w5xd/RC1101/PCBpartial.jpg

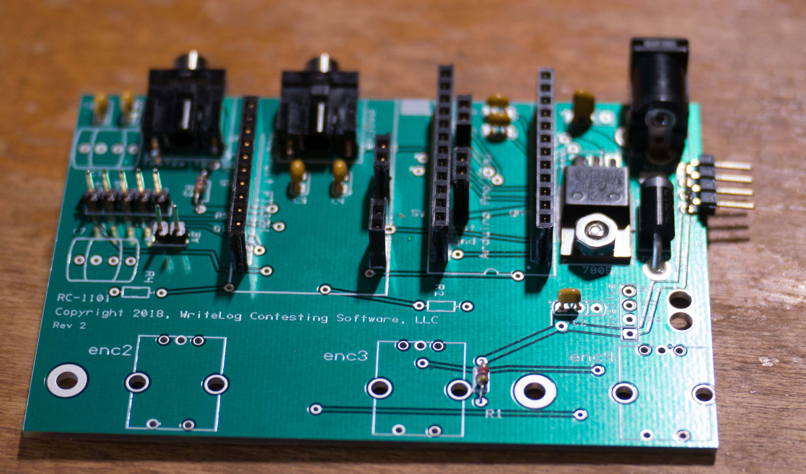
PCBpartial.jpg
