w5xd/RC1101/CAD/Trellis/Overlay-Blank.stp

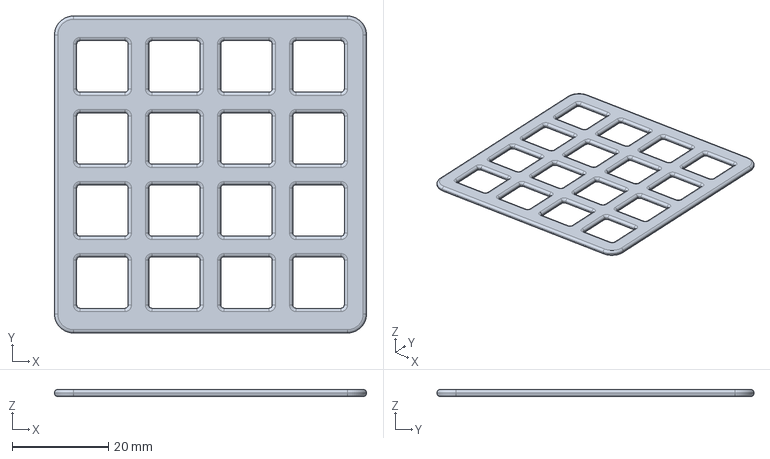
[picture p26: CAD file, 2024-01-12]
CAD/Trellis/Overlay-Blank.stp
65.0 x 66.0 x 1.50 mm
