w5xd/RC1101/STL/Overlay-Generic.STL

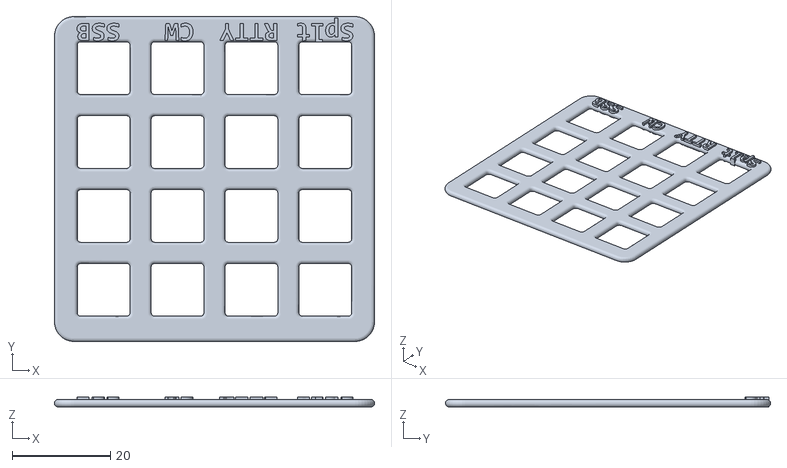
[picture p27: CAD file, 2022-08-31]
STL/Overlay-Generic.STL
65.0 x 66.0 x 2.00
