w5xd/RC1101/CAD/Adafruit232H/StandingOff.SLDPRT

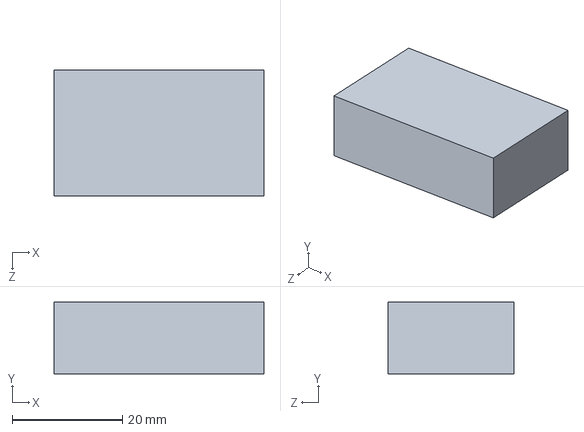
[picture p28: CAD file, 2020-03-09]
CAD/Adafruit232H/StandingOff.SLDPRT
38.1 x 13.0 x 22.9 mm
