w5xd/RC1101/CAD/Enclosure/enclosure2 LCD back cover.sldprt

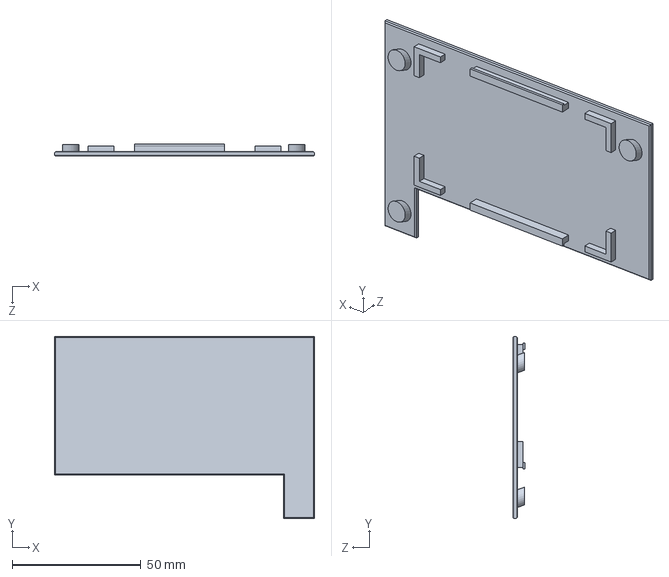
[picture p29: CAD file, 2019-06-19]
CAD/Enclosure/enclosure2 LCD back cover.sldprt
101.0 x 70.7 x 4.75 mm
