w5xd/RC1101/CAD/knobs/SmallKnob.SLDPRT

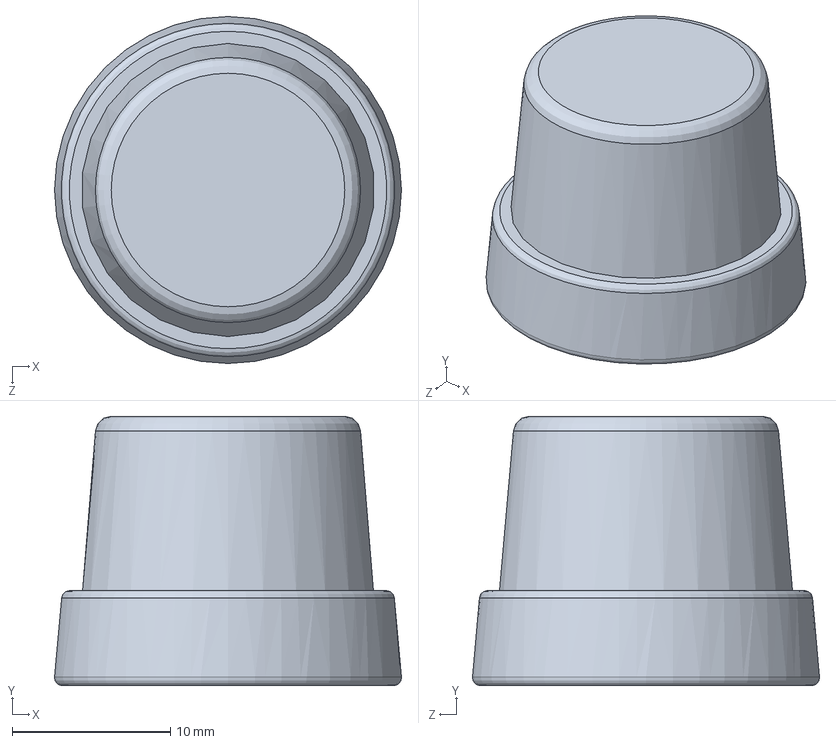
[picture p30: CAD file, 2019-06-19]
CAD/knobs/SmallKnob.SLDPRT
21.9 x 17.0 x 21.9 mm
