w5xd/RC1101/CAD/PCB/puiaudio.SLDPRT

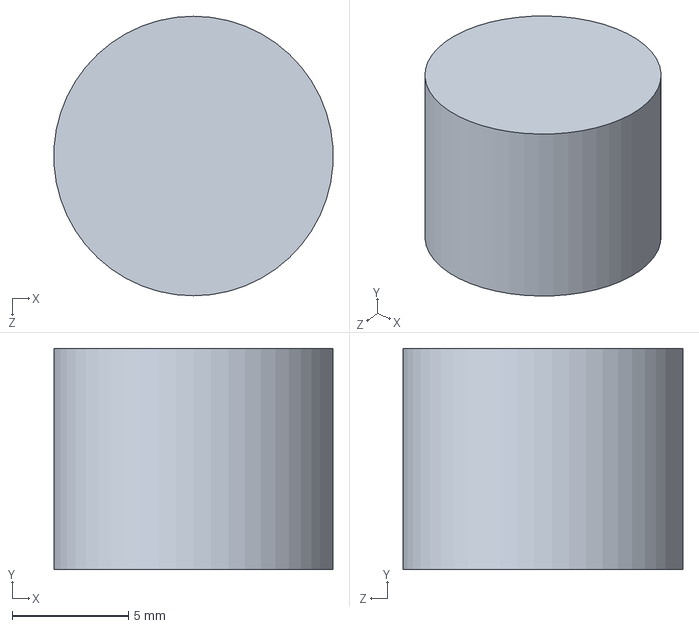
[picture p31: CAD file, 2019-06-19]
CAD/PCB/puiaudio.SLDPRT
12.0 x 9.50 x 12.0 mm
