w5xd/RC1101/CAD/pec12/pec12-encoder.SLDPRT

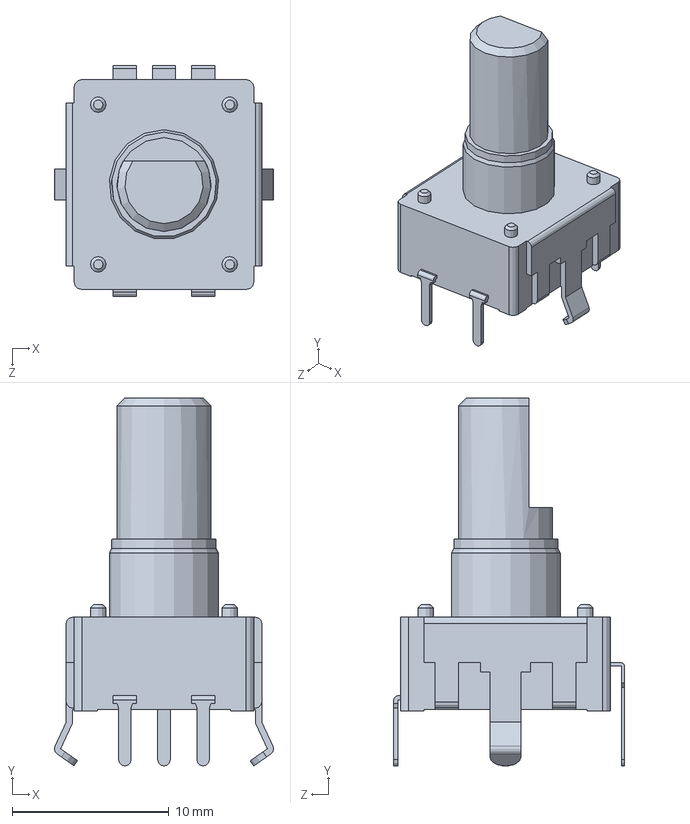
[picture p32: CAD file, 2019-06-19]
CAD/pec12/pec12-encoder.SLDPRT
14.0 x 23.5 x 14.8 mm
