w5xd/RC1101/CAD/TO220/274-2AB HEATSINK LOW HEIGHT BLK TO-220.SLDPRT

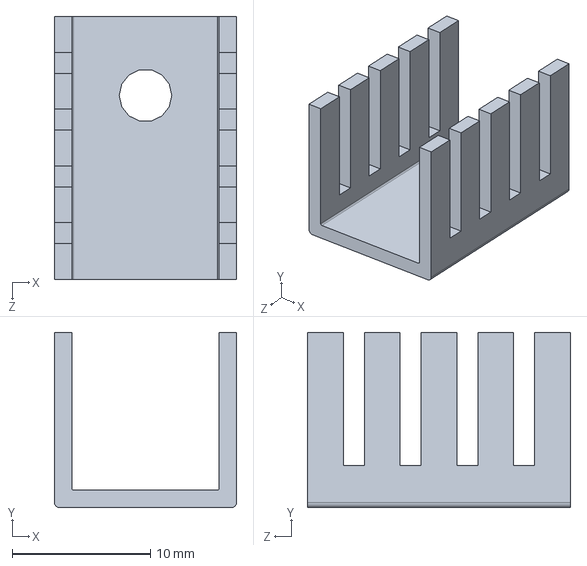
[picture p33: CAD file, 2018-12-13]
CAD/TO220/274-2AB HEATSINK LOW HEIGHT BLK TO-220.SLDPRT
13.2 x 12.7 x 19.1 mm
