w5xd/RC1101/CAD/Enclosure/enclosure2 bottom cover.sldprt

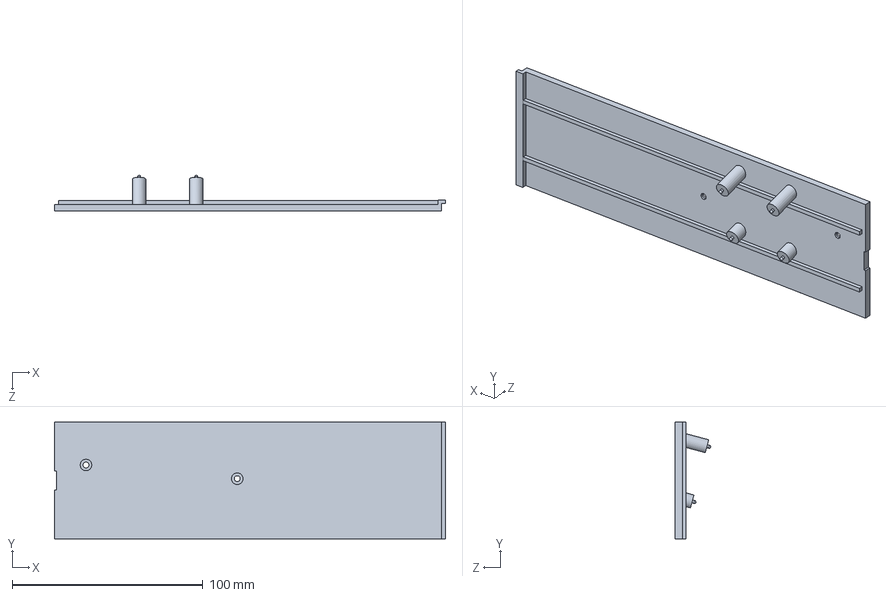
[picture p35: CAD file, 2019-06-19]
CAD/Enclosure/enclosure2 bottom cover.sldprt
205.2 x 61.2 x 18.7 mm
