w5xd/RC1101/CAD/PCB/5PinLcd.SLDPRT

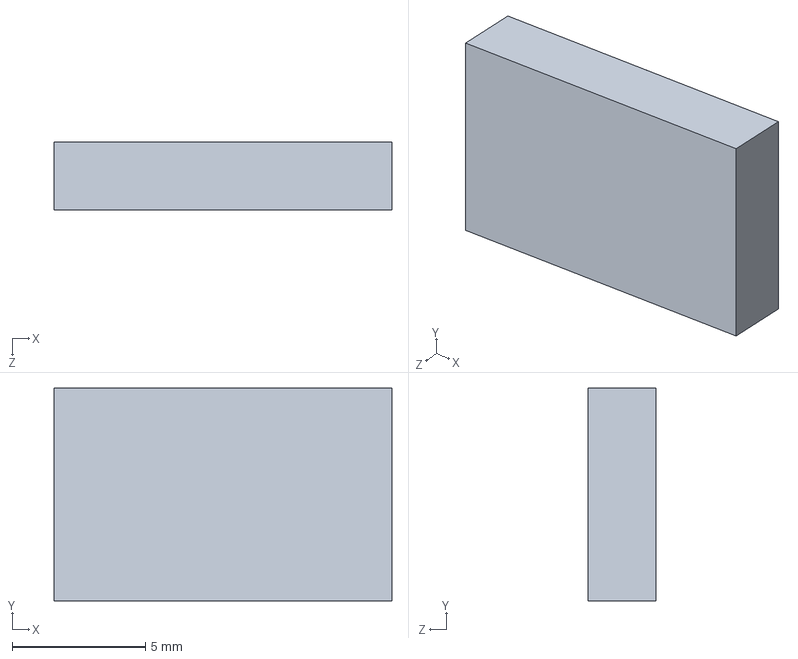
[picture p36: CAD file, 2019-06-19]
CAD/PCB/5PinLcd.SLDPRT
12.7 x 8.00 x 2.54 mm
