w5xd/RC1101/CAD/pec12/CUI_PJ-202A.sldprt

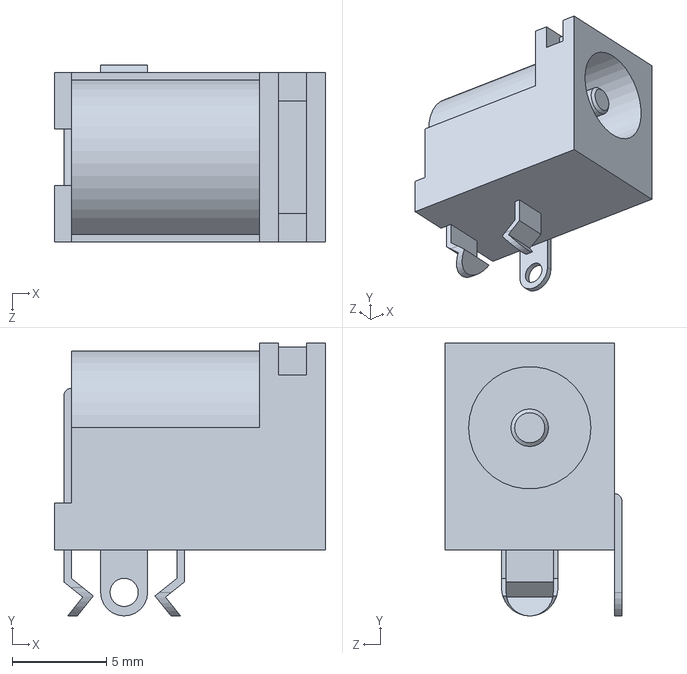
[picture p37: CAD file, 2019-06-19]
CAD/pec12/CUI_PJ-202A.sldprt
14.4 x 14.5 x 9.40 mm
