w5xd/RC1101/CAD/Trellis/Overlay-Icom.SLDPRT

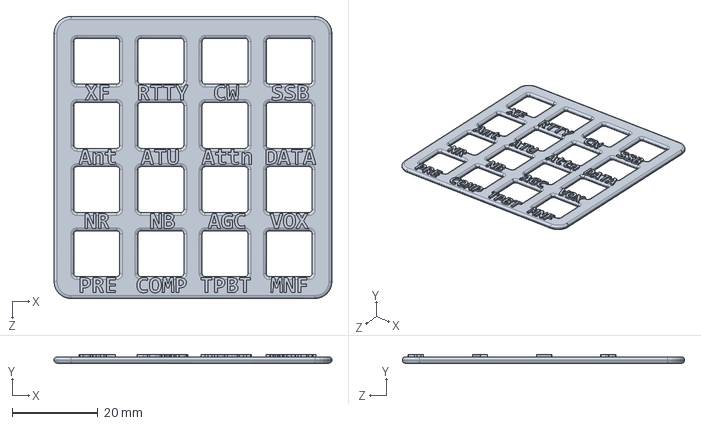
[picture p38: CAD file, 2022-08-31]
CAD/Trellis/Overlay-Icom.SLDPRT
65.0 x 2.00 x 66.0 mm
