w5xd/RC1101/CAD/Adafruit232H/quiik.stp

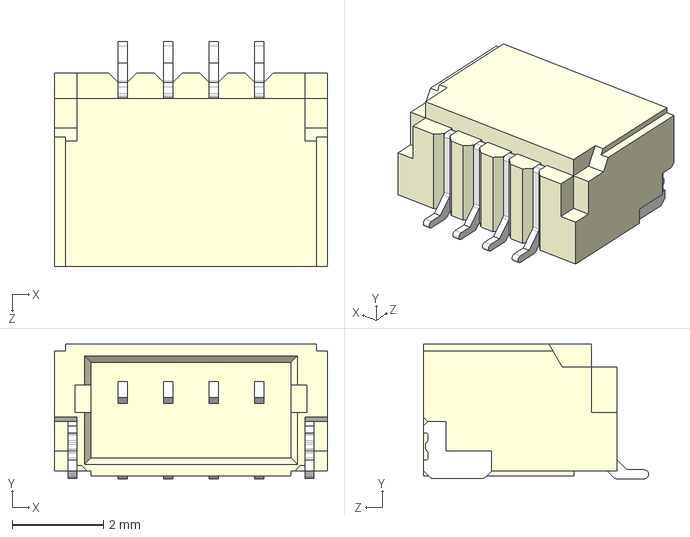
[picture p39: CAD file, 2020-03-09]
CAD/Adafruit232H/quiik.stp
6.00 x 2.96 x 4.95 mm
