w5xd/RC1101/CAD/LCD/gen4/4DLCD-32T-QVGA-LCDGLASS.sldprt

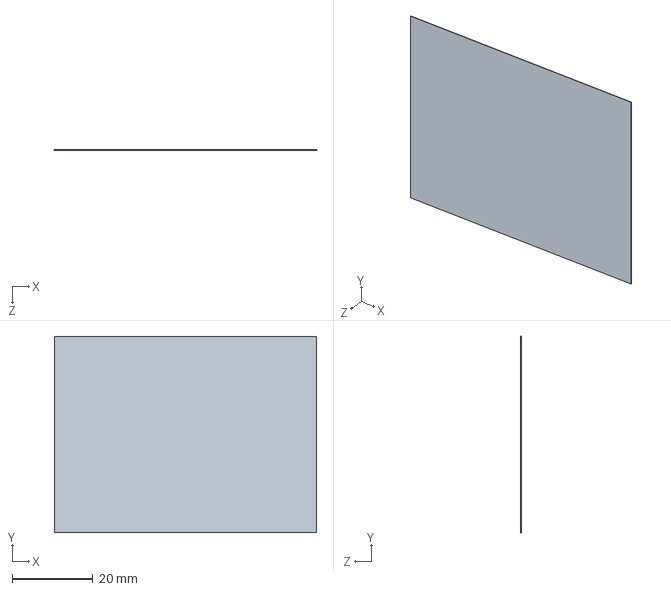
[picture p40: CAD file, 2019-06-19]
CAD/LCD/gen4/4DLCD-32T-QVGA-LCDGLASS.sldprt
64.8 x 48.6 x 0.1 mm
