w5xd/RC1101/CAD/PCB/Enc1Header.SLDPRT

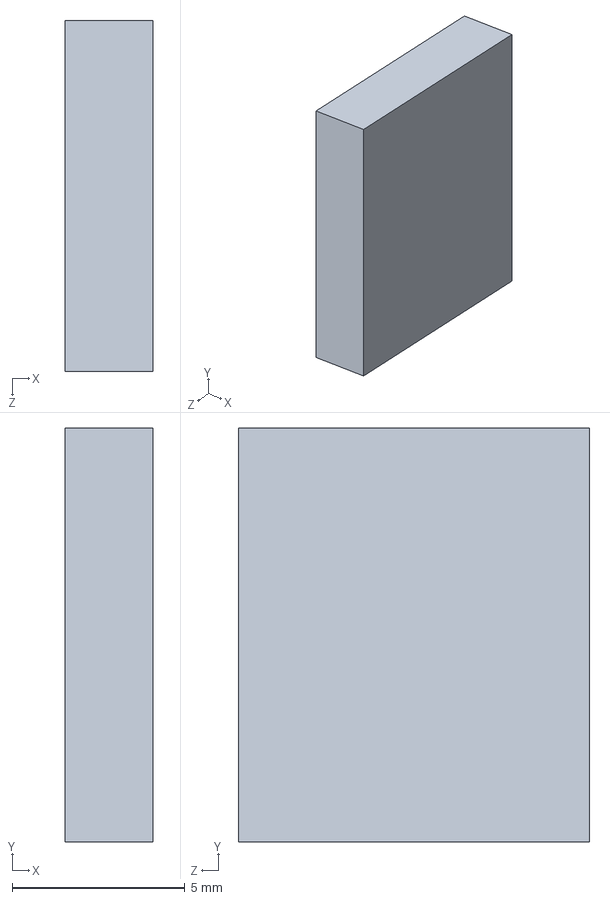
[picture p41: CAD file, 2019-06-19]
CAD/PCB/Enc1Header.SLDPRT
2.54 x 12.0 x 10.2 mm
