w5xd/RC1101/CAD/Adafruit232H/pcb-ft232.SLDPRT

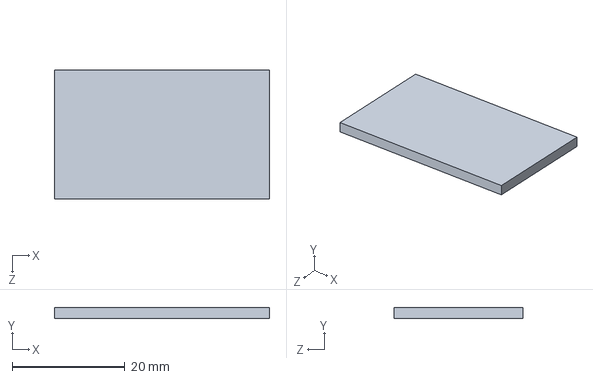
[picture p42: CAD file, 2020-03-09]
CAD/Adafruit232H/pcb-ft232.SLDPRT
38.1 x 2.00 x 22.9 mm
