w5xd/RC1101/CAD/PCB/gen4-ib.SLDPRT

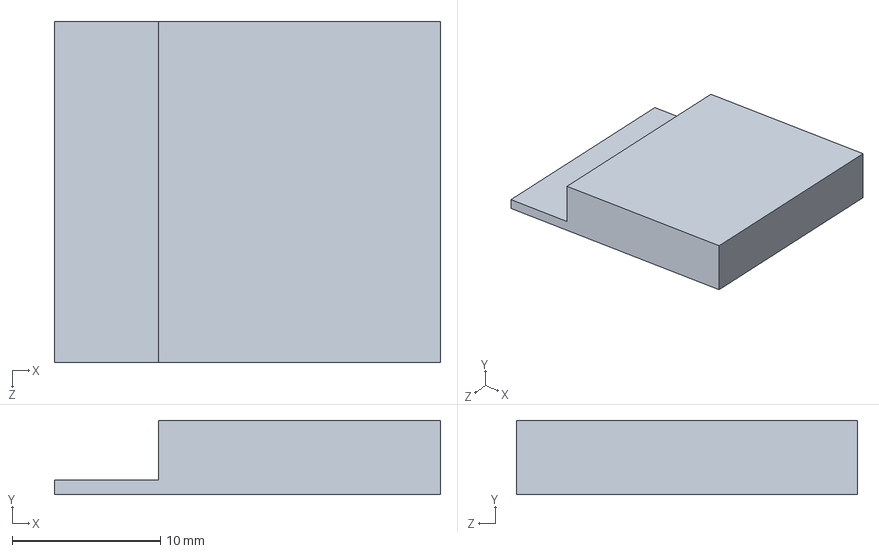
[picture p43: CAD file, 2019-06-19]
CAD/PCB/gen4-ib.SLDPRT
26.0 x 5.00 x 23.0 mm
