w5xd/RC1101/CAD/Adafruit232H/USB-C.stp

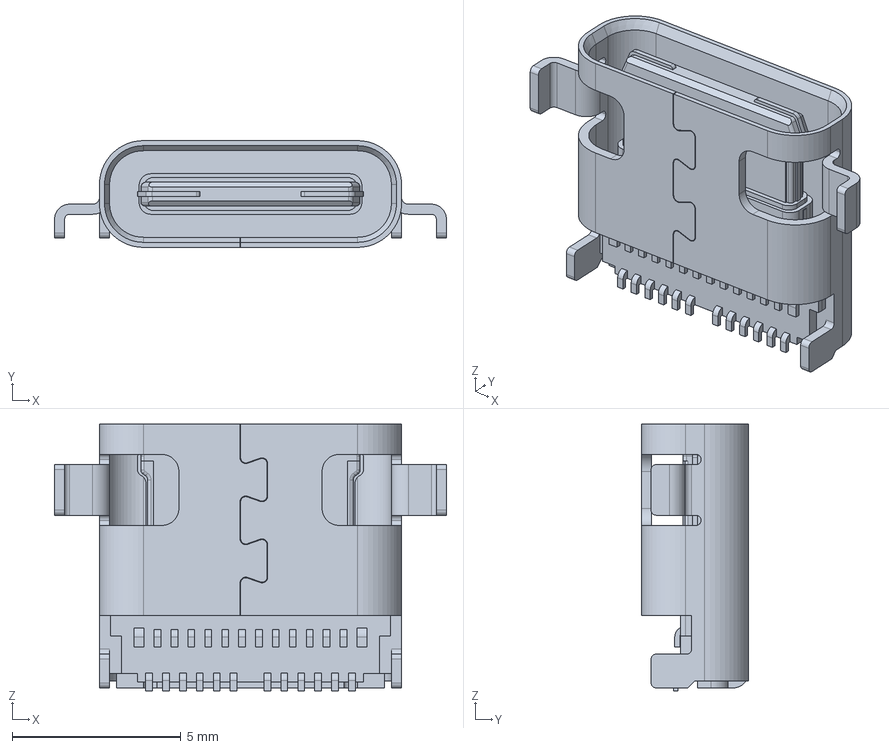
[picture p44: CAD file, 2020-03-09]
CAD/Adafruit232H/USB-C.stp
11.6 x 3.16 x 7.90 mm
