w5xd/RC1101/CAD/LCD/gen4/4DLCD-32T-QVGA-METAL.sldprt

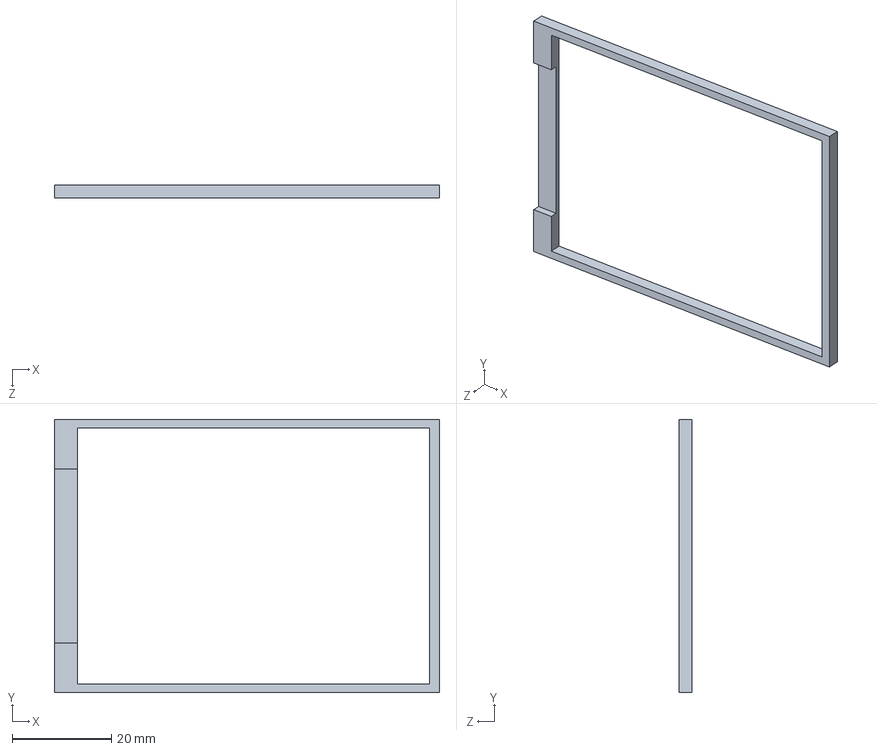
[picture p45: CAD file, 2019-06-19]
CAD/LCD/gen4/4DLCD-32T-QVGA-METAL.sldprt
77.6 x 55.0 x 2.65 mm
