w5xd/RC1101/CAD/PCB/PCB.SLDPRT

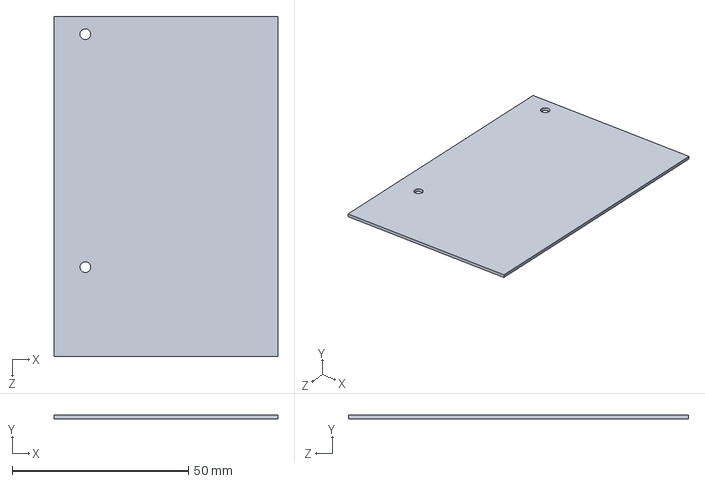
[picture p46: CAD file, 2019-06-19]
CAD/PCB/PCB.SLDPRT
63.5 x 1.00 x 96.5 mm
