w5xd/RC1101/STL/Overlay-Flex6000.STL

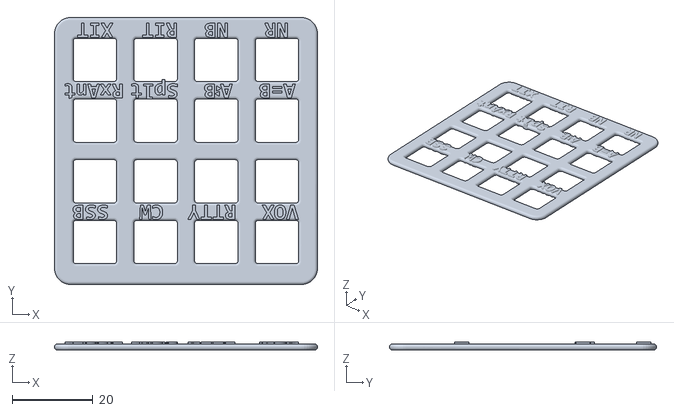
[picture p47: CAD file, 2022-08-31]
STL/Overlay-Flex6000.STL
65.0 x 66.0 x 2.00
