w5xd/RC1101/CAD/Trellis/Adafruit Trellis 3mm.SLDPRT

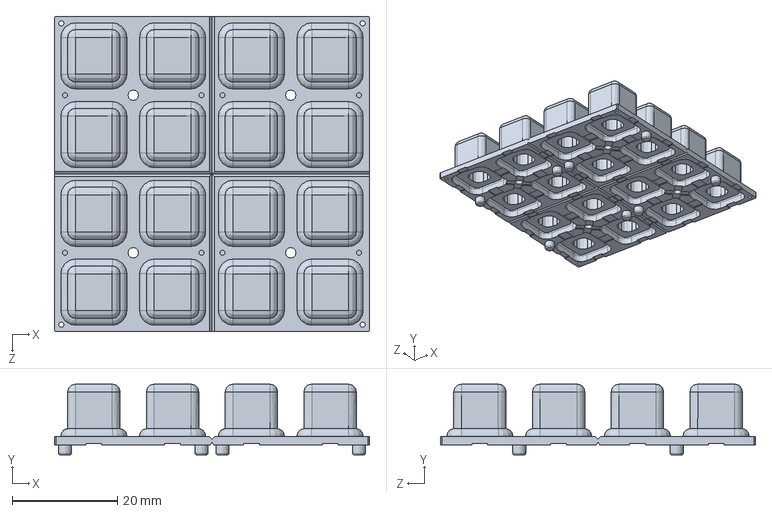
[picture p48: CAD file, 2019-06-19]
CAD/Trellis/Adafruit Trellis 3mm.SLDPRT
60.0 x 13.5 x 60.0 mm
