w5xd/RC1101/STL/enclosure42.STL

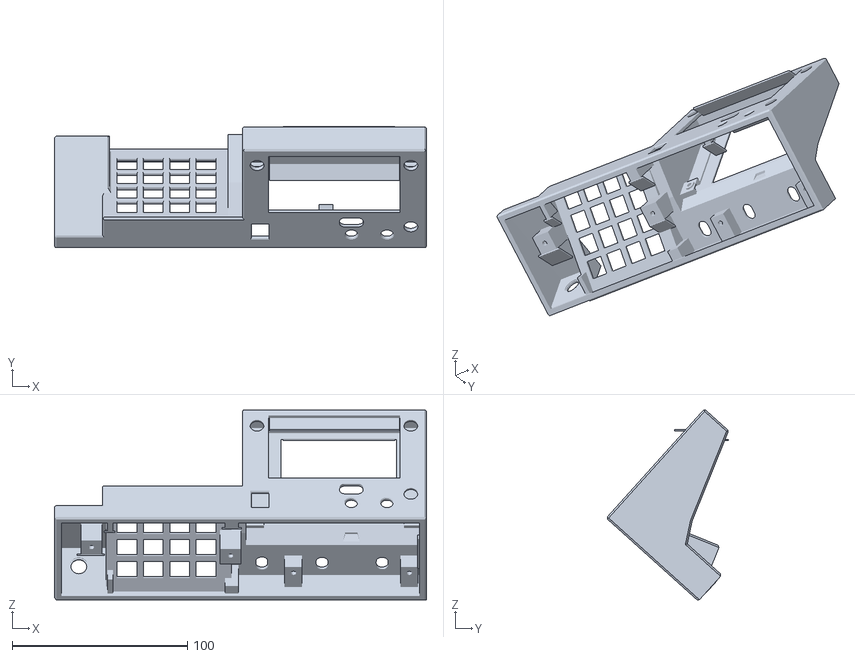
[picture p49: CAD file, 2022-08-31]
STL/enclosure42.STL
212.2 x 69.2 x 108.2
