w5xd/RC1101/CAD/LCD/gen4/4DLCD-32T-QVGA-BASE.sldprt

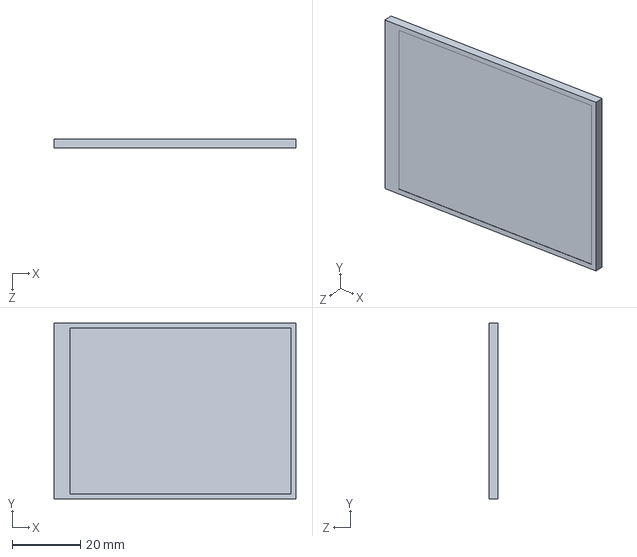
[picture p50: CAD file, 2019-06-19]
CAD/LCD/gen4/4DLCD-32T-QVGA-BASE.sldprt
71.0 x 51.6 x 2.65 mm
